fenr1r/IV-16_clock/Controller_program/GccApp1_Atmega328P/TC62D748.hpp

/*
 * TC62D748.hpp
 *
 * Created: 2025/10/13 20:03:03
 *  Author: fenrir_
 */ 

#include "time.hpp"

void TC62D748_init();
void TC62D748_send(const time);

void TC62D748_EnableDisplay();
void TC62D748_DisableDisplay();
